Atlantis-Specialist-Technologies/CAN485/Examples/JTAG_Software_Disable/JTAG_Software_Disable.ino

void setup() {
  // Disable JTAG
  // Note there is an open issue regarding this code.
  // Refer to the link below for further details.
  // So far it works in all tests. 
  // https://github.com/Atlantis-Specialist-Technologies/CAN485/issues/2

  // A timed sequence must be followed in order to disable JTAG.
  // The JTD bit must be written twice within 4 cycles
  
  MCUCR = (1<<JTD);         // Write JTD bit
  MCUCR = (1<<JTD);         // Write again within 4 cycles

  // Set JTAG pins as outputs
  pinMode(A4, OUTPUT);
  pinMode(A5, OUTPUT);
  pinMode(A6, OUTPUT);
  pinMode(A7, OUTPUT);
}

void loop() {
  // Blink the JTAG pins to test them
  digitalWrite(A4, HIGH);
  digitalWrite(A5, HIGH);
  digitalWrite(A6, HIGH);
  digitalWrite(A7, HIGH);
  delay(1000);
  digitalWrite(A4, LOW);
  digitalWrite(A5, LOW);
  digitalWrite(A6, LOW);
  digitalWrite(A7, LOW);
  delay(1000);
}
