Atlantis-Specialist-Technologies/CAN485/Firmware/ast/avr/bootloaders/can485-boot/pin_defs.h

/*
 * pin_defs.h
 * optiboot helper defining the default pin assignments (LED, SOFT_UART)
 * for the various chips that are supported.  This also has some ugly macros
 * for selecting among various UARTs and LED possibilities using command-line
 * defines like "UART=2 LED=B5"
 *
 * Copyright 2013-2015 by Bill Westfield.
 * Copyright 2010 by Peter Knight.
 * This software is licensed under version 2 of the Gnu Public License.
 * See optiboot.c for details.
 */

/**********************************************************/
/* Modified by Atlantis Specialist Technologies
/* by James Blakey-Milner, 1 Aug 2017.
/* Added support for the AST CAN485 board
/* Note! AST modifications are in early development (alpha)
/* and are likely to change without notice.
/**********************************************************/
 
/*------------------------------------------------------------------------ */
#if defined(__AVR_ATmega168__) || defined(__AVR_ATmega168P__) || defined(__AVR_ATmega328__) || defined(__AVR_ATmega328P__) || defined(__AVR_ATmega88) || defined(__AVR_ATmega8__) || defined(__AVR_ATmega88__)
/*------------------------------------------------------------------------ */

/* Onboard LED is connected to pin PB5 in Arduino NG, Diecimila, and Duemilanove
 */ 
#if !defined(LED)
#define LED B5
#endif

/* Ports for soft UART */
#ifdef SOFT_UART
#define UART_PORT   PORTD
#define UART_PIN    PIND
#define UART_DDR    DDRD
#define UART_TX_BIT 1
#define UART_RX_BIT 0
#endif
#endif

/*
 * Handle devices with up to 4 uarts (eg m1280.)  Rather inelegantly.
 * Note that mega8/m32 still needs special handling, because ubrr is handled
 * differently.
 */
#if UART == 0
# define UART_SRA UCSR0A
# define UART_SRB UCSR0B
# define UART_SRC UCSR0C
# define UART_SRL UBRR0L
# define UART_UDR UDR0
#elif UART == 1
#if !defined(UDR1)
#error UART == 1, but no UART1 on device
#endif
# define UART_SRA UCSR1A
# define UART_SRB UCSR1B
# define UART_SRC UCSR1C
# define UART_SRL UBRR1L
# define UART_UDR UDR1
#elif UART == 2
#if !defined(UDR2)
#error UART == 2, but no UART2 on device
#endif
# define UART_SRA UCSR2A
# define UART_SRB UCSR2B
# define UART_SRC UCSR2C
# define UART_SRL UBRR2L
# define UART_UDR UDR2
#elif UART == 3
#if !defined(UDR3)
#error UART == 3, but no UART3 on device
#endif
# define UART_SRA UCSR3A
# define UART_SRB UCSR3B
# define UART_SRC UCSR3C
# define UART_SRL UBRR3L
# define UART_UDR UDR3
#endif

#if defined(__AVR_ATmega8__) || defined (__AVR_ATmega32__) || defined (__AVR_ATmega16__)
  //Name conversion R.Wiersma
  #define UCSR0A	UCSRA
  #define UDR0 		UDR
  #define UDRE0 	UDRE
  #define RXC0		RXC
  #define FE0           FE
  #define TIFR1 	TIFR
  #define WDTCSR	WDTCR
#endif
#if defined (__AVR_ATmega32__) || defined (__AVR_ATmega16__)
  #define WDCE		WDTOE
#endif

/* Luminet support */
/*------------------------------------------------------------------------ */
#if defined(__AVR_ATtiny84__)
/*------------------------------------------------------------------------ */
/* Red LED is connected to pin PA4 */ 
#if !defined(LED)
#define LED         A4
#endif

/* Ports for soft UART - left port only for now. TX/RX on PA2/PA3 */
#ifdef SOFT_UART
#define UART_PORT   PORTA
#define UART_PIN    PINA
#define UART_DDR    DDRA
#define UART_TX_BIT 2
#define UART_RX_BIT 3
#endif
#endif

/*------------------------------------------------------------------------ */
/* Sanguino support (and other 40pin DIP cpus) */
#if defined(__AVR_ATmega644P__) || defined(__AVR_ATmega1284P__) || defined(__AVR_ATmega32__) || defined (__AVR_ATmega16__)
/*------------------------------------------------------------------------ */
/* Onboard LED is connected to pin PB0 on Sanguino */ 
#if !defined(LED)
#define LED         B0
#endif

/* Ports for soft UART */
#ifdef SOFT_UART
#define UART_PORT   PORTD
#define UART_PIN    PIND
#define UART_DDR    DDRD
#define UART_TX_BIT 1
#define UART_RX_BIT 0
#endif
#endif

/*------------------------------------------------------------------------ */
/* Mega support */
#if defined(__AVR_ATmega1280__)
/*------------------------------------------------------------------------ */
/* Onboard LED is connected to pin PB7 on Arduino Mega */ 
#if !defined(LED)
#define LED         B7
#endif

/* Ports for soft UART */
#ifdef SOFT_UART
#define UART_PORT   PORTE
#define UART_PIN    PINE
#define UART_DDR    DDRE
#define UART_TX_BIT 1
#define UART_RX_BIT 0
#endif
#endif

/*------------------------------------------------------------------------ */
/* AST - can485 */
#if defined(__AVR_AT90CAN128__)
/* On-board LED is connected to pin PB1 */
#if !defined(LED)
#define LED B1
#endif
/* Rename watchdog control register */
#define WDTCSR	WDTCR

#endif





/*
 * ------------------------------------------------------------------------
 * A bunch of macros to enable the LED to be specified as "B5" for bit 5 
 * of port B, and similar.
 */
#if 1
/* allows these to be collapsed in atmel studio IDE*/
#define A0 0x100
#define A1 0x101
#define A2 0x102
#define A3 0x103
#define A4 0x104
#define A5 0x105
#define A6 0x106
#define A7 0x107

#define B0 0x200
#define B1 0x201
#define B2 0x202
#define B3 0x203
#define B4 0x204
#define B5 0x205
#define B6 0x206
#define B7 0x207

#define C0 0x300
#define C1 0x301
#define C2 0x302
#define C3 0x303
#define C4 0x304
#define C5 0x305
#define C6 0x306
#define C7 0x307

#define D0 0x400
#define D1 0x401
#define D2 0x402
#define D3 0x403
#define D4 0x404
#define D5 0x405
#define D6 0x406
#define D7 0x407

#define E0 0x500
#define E1 0x501
#define E2 0x502
#define E3 0x503
#define E4 0x504
#define E5 0x505
#define E6 0x506
#define E7 0x507

#define F0 0x600
#define F1 0x601
#define F2 0x602
#define F3 0x603
#define F4 0x604
#define F5 0x605
#define F6 0x606
#define F7 0x607

#define G0 0x700
#define G1 0x701
#define G2 0x702
#define G3 0x703
#define G4 0x704
#define G5 0x705
#define G6 0x706
#define G7 0x707

#define H0 0x800
#define H1 0x801
#define H2 0x802
#define H3 0x803
#define H4 0x804
#define H5 0x805
#define H6 0x806
#define H7 0x807

#define J0 0xA00
#define J1 0xA01
#define J2 0xA02
#define J3 0xA03
#define J4 0xA04
#define J5 0xA05
#define J6 0xA06
#define J7 0xA07

#define K0 0xB00
#define K1 0xB01
#define K2 0xB02
#define K3 0xB03
#define K4 0xB04
#define K5 0xB05
#define K6 0xB06
#define K7 0xB07

#define L0 0xC00
#define L1 0xC01
#define L2 0xC02
#define L3 0xC03
#define L4 0xC04
#define L5 0xC05
#define L6 0xC06
#define L7 0xC07



#if LED == B0
#undef LED
#define LED_DDR     DDRB
#define LED_PORT    PORTB
#define LED_PIN     PINB
#define LED	    PINB0
#elif LED == B1
#undef LED
#define LED_DDR     DDRB
#define LED_PORT    PORTB
#define LED_PIN     PINB
#define LED	    PINB1
#elif LED == B2
#undef LED
#define LED_DDR     DDRB
#define LED_PORT    PORTB
#define LED_PIN     PINB
#define LED	    PINB2
#elif LED == B3
#undef LED
#define LED_DDR     DDRB
#define LED_PORT    PORTB
#define LED_PIN     PINB
#define LED	    PINB3
#elif LED == B4
#undef LED
#define LED_DDR     DDRB
#define LED_PORT    PORTB
#define LED_PIN     PINB
#define LED	    PINB4
#elif LED == B5
#undef LED
#define LED_DDR     DDRB
#define LED_PORT    PORTB
#define LED_PIN     PINB
#define LED	    PINB5
#elif LED == B6
#undef LED
#define LED_DDR     DDRB
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
#undef LED
#define LED_DDR     DDRA
#define LED_PORT    PORTA
#define LED_PIN     PINA
#define LED	    PINA7

#else
#error -------------------------------------------
#error Unrecognized LED name.  Should be like "B5"
#error -------------------------------------------
#endif

#endif
